SeeedDocument/BeagleBone_Green_Wireless/images/bbgw_drawing_1.png

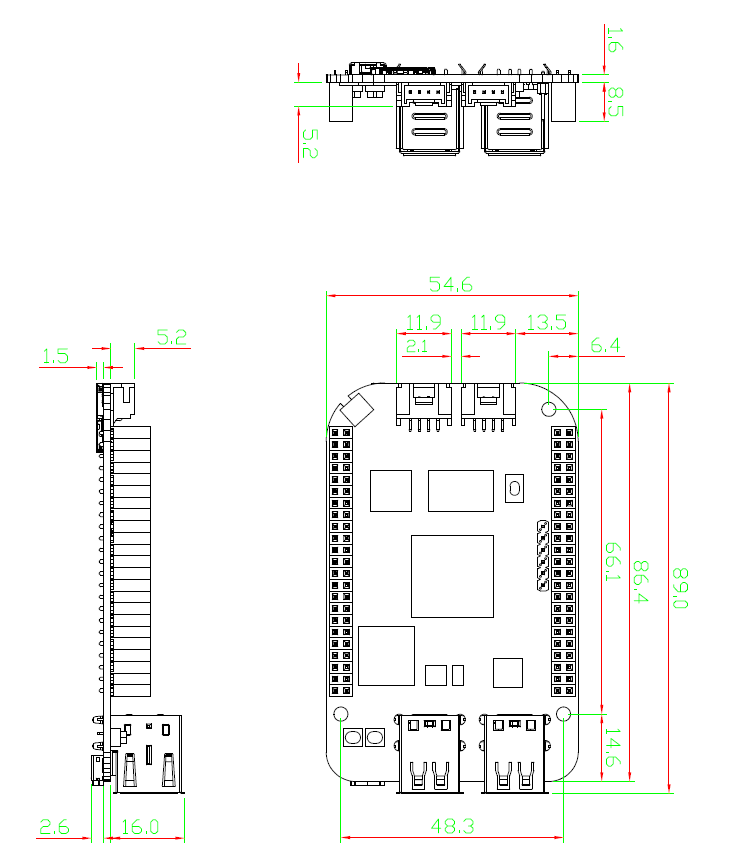
images/bbgw_drawing_1.png
