SeeedDocument/BeagleBone_Green_Wireless/images/bbgw_drawing_2.png

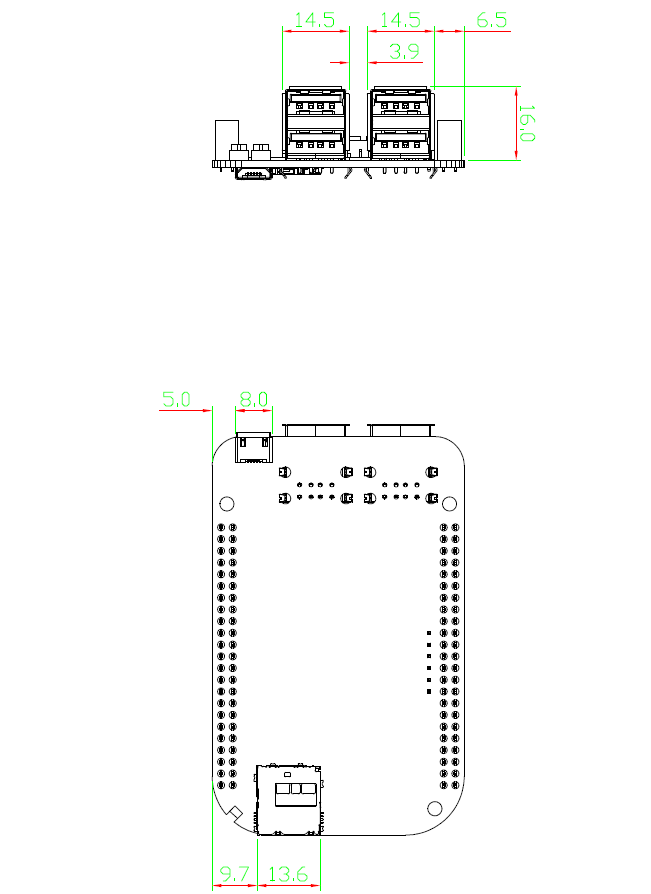
images/bbgw_drawing_2.png
